Janelle-Duenas/POV_MIP/SolidWorks files/plastic parts/3D-printed/Wire Mount.SLDPRT

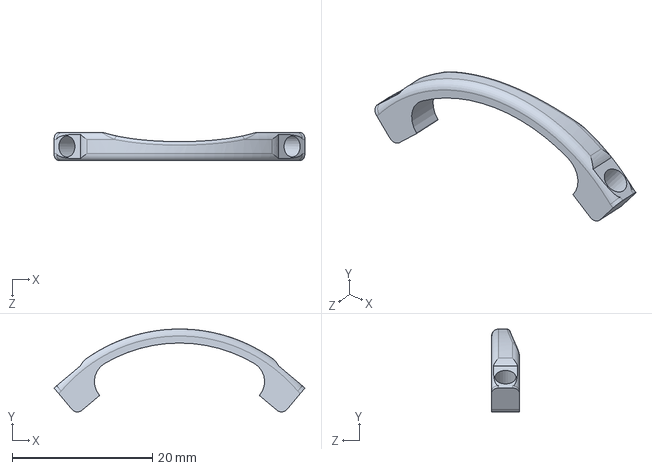
[picture p14: CAD file, 2018-06-08]
SolidWorks files/plastic parts/3D-printed/Wire Mount.SLDPRT
35.8 x 11.8 x 4.00 mm
