Janelle-Duenas/POV_MIP/SolidWorks files/plastic parts/3D-printed/Motor Mount.SLDPRT

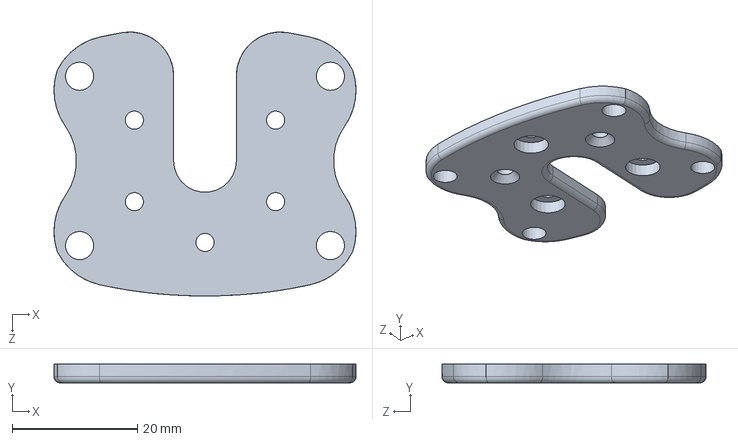
[picture p15: CAD file, 2018-06-08]
SolidWorks files/plastic parts/3D-printed/Motor Mount.SLDPRT
48.2 x 3.00 x 42.1 mm
